SaBuMa/MEDICION-DE-CALIDAD-DE-ENERG-A-DE-UN-INVERSOR-SINCRONIZADO-CON-LA-LINEA-COMERCIAL/PLL/Simulacion/ctolinea.jpg

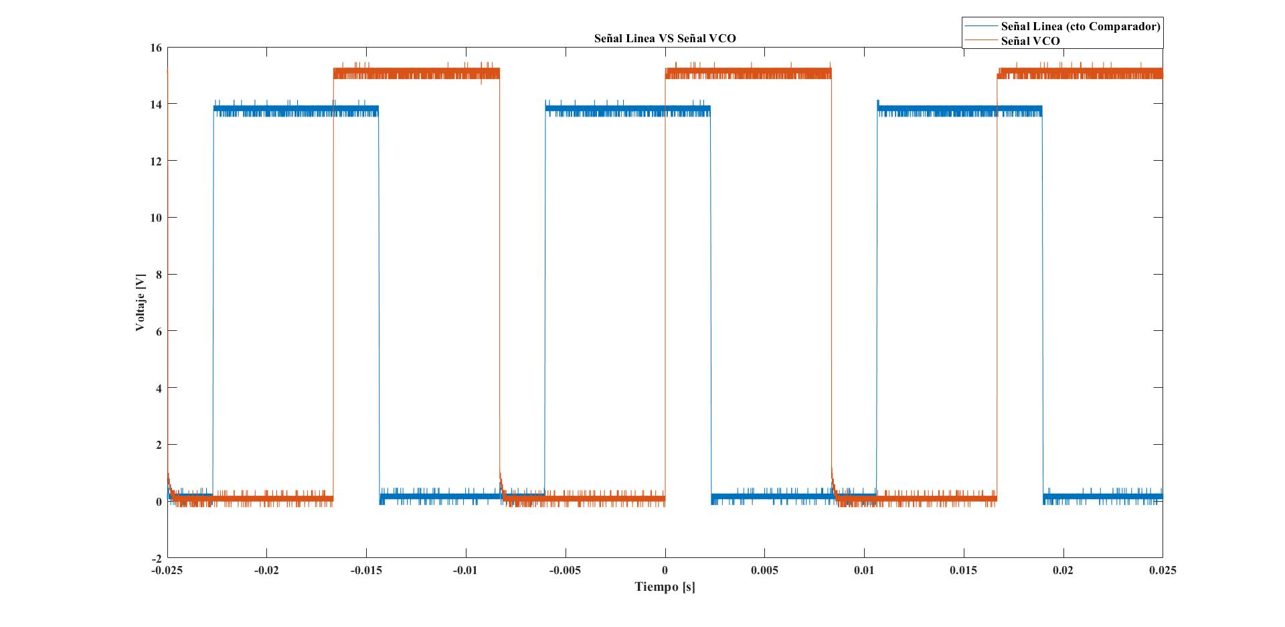
PLL/Simulacion/ctolinea.jpg
