SaBuMa/MEDICION-DE-CALIDAD-DE-ENERG-A-DE-UN-INVERSOR-SINCRONIZADO-CON-LA-LINEA-COMERCIAL/PLL/Simulacion/pll32.jpg

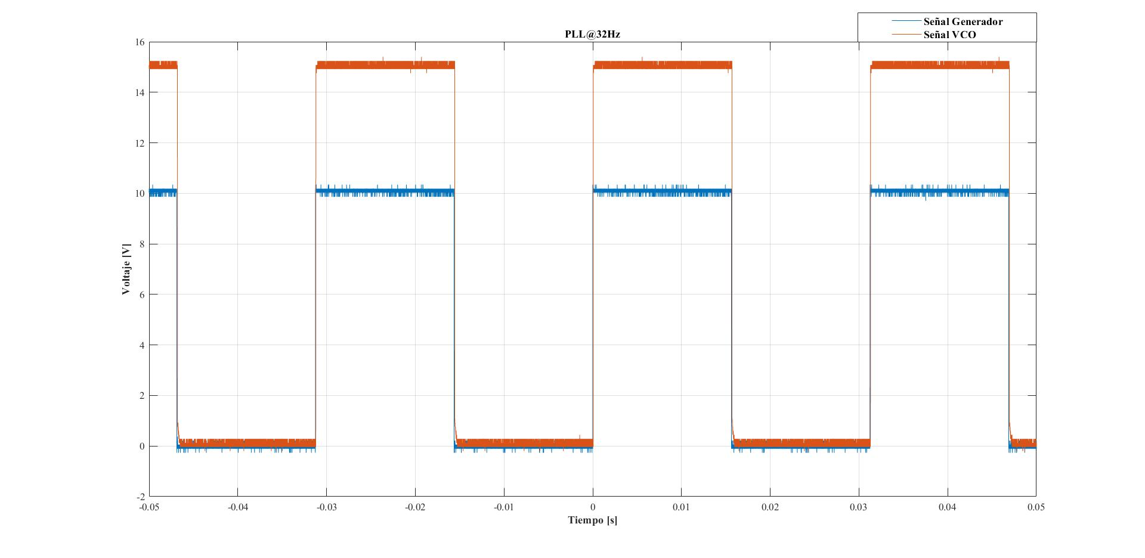
PLL/Simulacion/pll32.jpg
