SaBuMa/MEDICION-DE-CALIDAD-DE-ENERG-A-DE-UN-INVERSOR-SINCRONIZADO-CON-LA-LINEA-COMERCIAL/PLL/Simulacion/tran.jpg

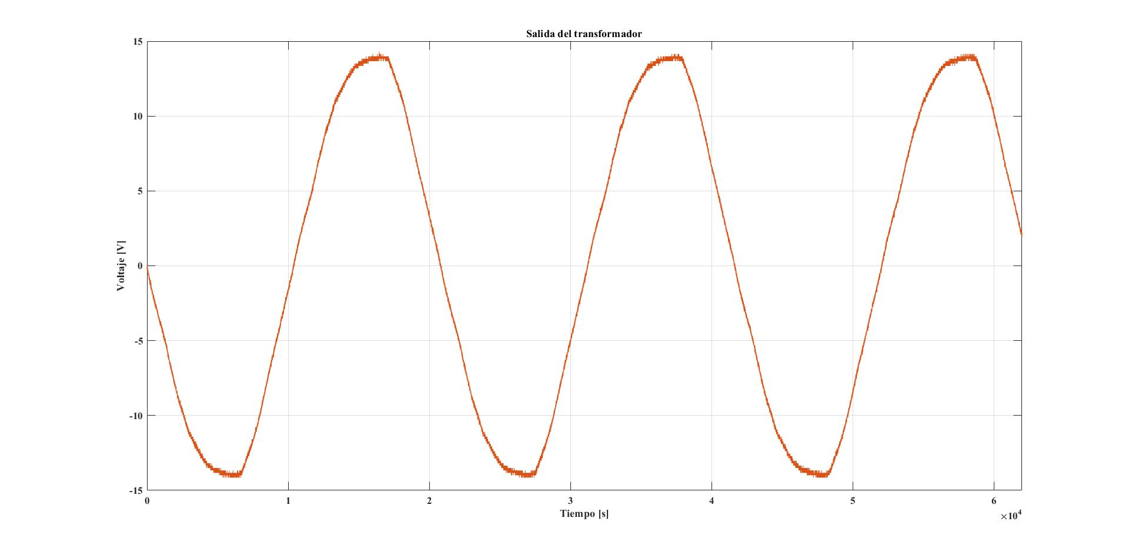
PLL/Simulacion/tran.jpg
