SaBuMa/MEDICION-DE-CALIDAD-DE-ENERG-A-DE-UN-INVERSOR-SINCRONIZADO-CON-LA-LINEA-COMERCIAL/VCO/Circuito VCO.asc

C1: cap; 82n
C2: cap; 1µ
C3: cap; 22µ
C4: cap; 1µ
D1: diode; 1N4148
D2: diode; 1N4148
D3: diode; 1N4148
Q1: npn; 2N2222
R1: res; 20k
R2: res; 10k
R3: res; 10k
R4: res; 10k
R5: res; 10k
R6: res; 10k
R7: res; 10k
R8: res; 10k
R9: res; 10k
R10: res; 10k
R11: res; 16k
R12: res; 160k
R13: res; 10k
R16: res; 1.5k
R17: res; 10k
R18: res; 15k
R19: res; 10k
R20: res; 20k
R21: res; 10k
R22: res; 10k
R23: res; 10k
R24: res; 20k
U1: UniversalOpamp2
U2: UniversalOpamp2
U3: UniversalOpamp2
U4: UniversalOpamp2
U5: UniversalOpamp2
U6: UniversalOpamp2
U7: UniversalOpamp2
U8: UniversalOpamp2
U9: UniversalOpamp2
V1: voltage; 15
V2: voltage; 8
V5: voltage; -15
Named nets: 0, Vcc, Vdc, vt, -vt, -15, Triangulo, Seno, -Vdc, Vo1, Vo2, Vo3, Vo4, Vp, Vn, Vc, Vo5, Vo6, +Vdc
.tran 0 320m 260m 0.1 startup uic
